dkonigsberg/nestronic/docs/render-1.png

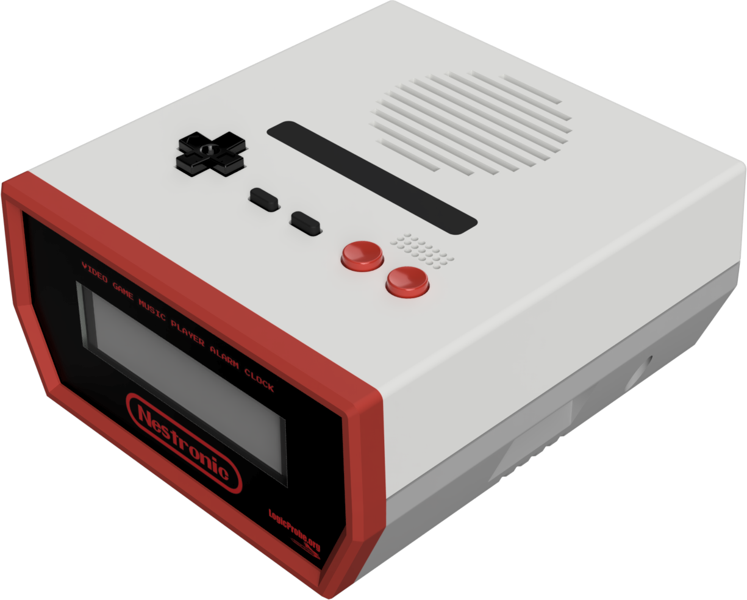
docs/render-1.png
