dkonigsberg/nestronic/docs/render-2.png

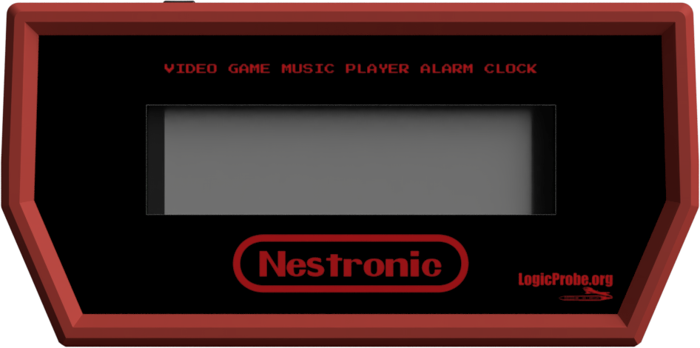
docs/render-2.png
