dkonigsberg/nestronic/docs/render-3.png

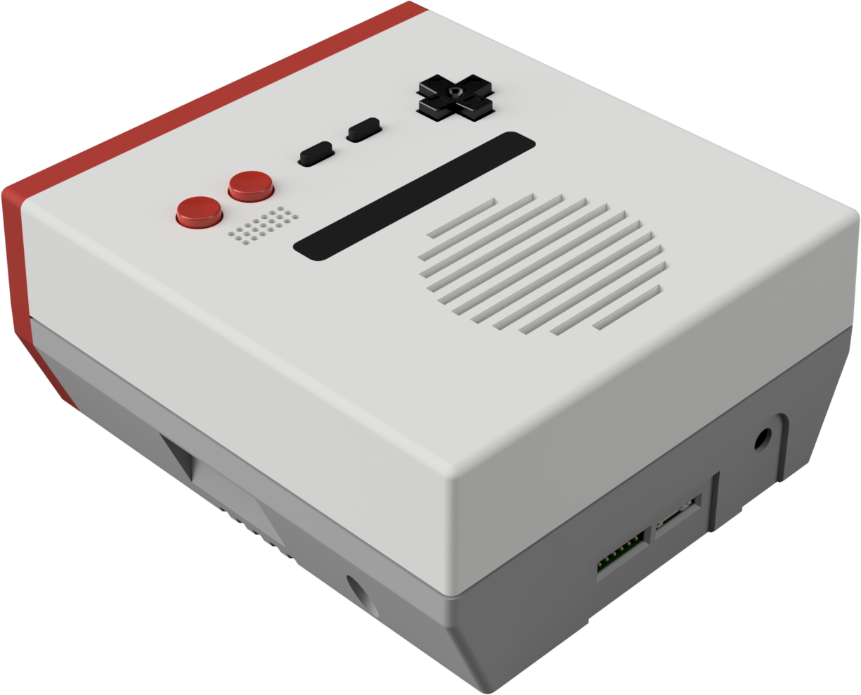
docs/render-3.png
