dkonigsberg/nestronic/docs/render-4.png

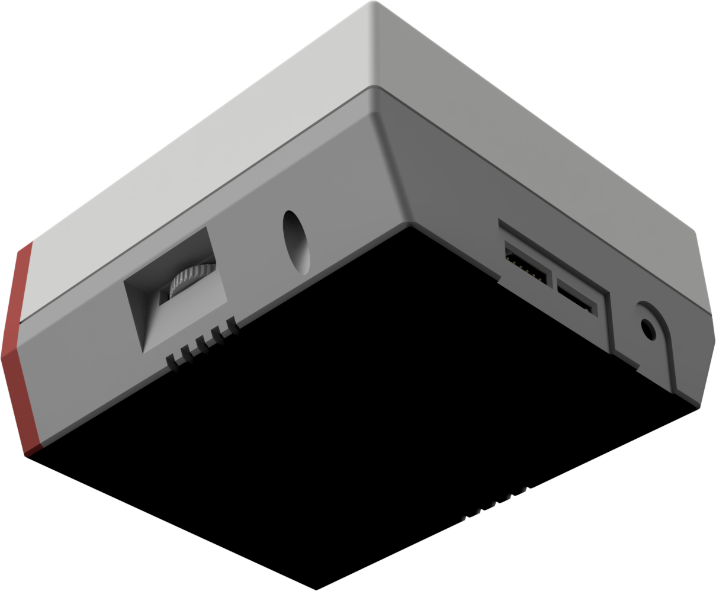
docs/render-4.png
