dkonigsberg/nestronic/hardware/3d_models/CUI_PJ-102AH.step

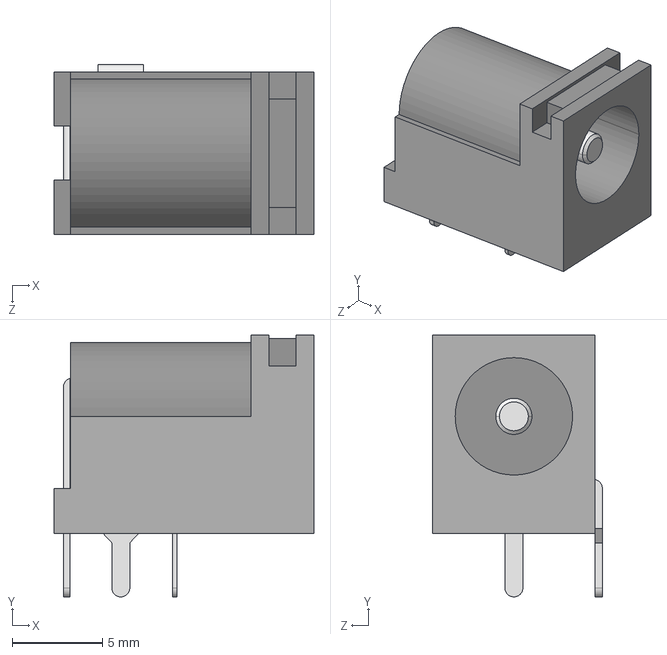
[picture p37: CAD file, 2018-06-15]
hardware/3d_models/CUI_PJ-102AH.step
14.4 x 14.5 x 9.40 mm
