dkonigsberg/nestronic/models/button_ab.step

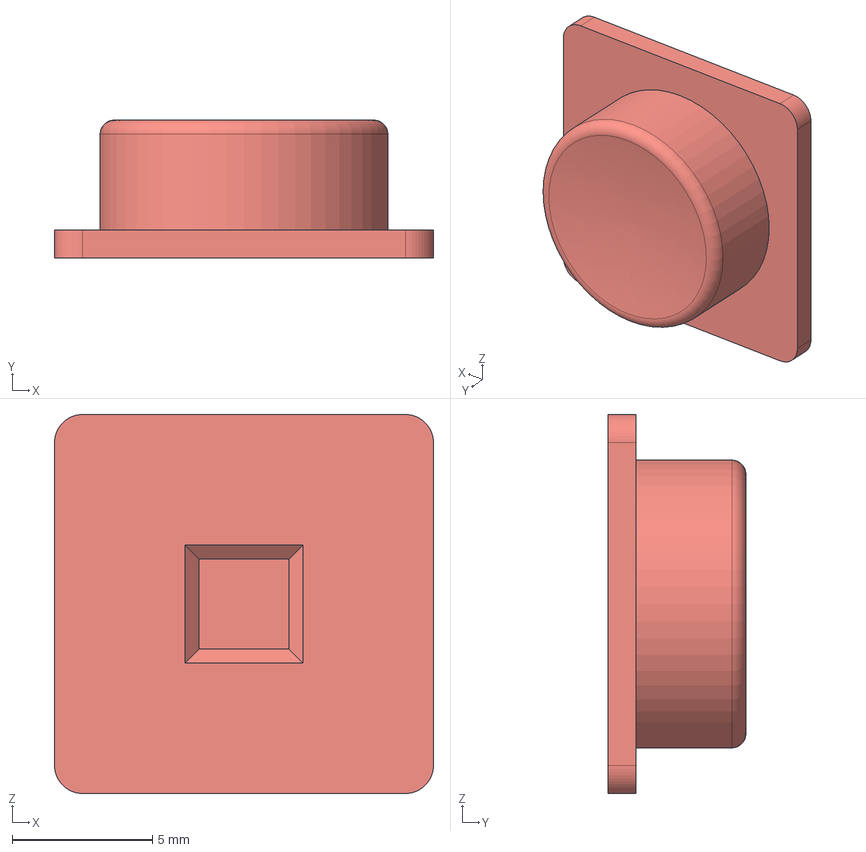
[picture p38: CAD file, 2018-06-17]
models/button_ab.step
13.5 x 4.91 x 13.5 mm
