dkonigsberg/nestronic/hardware/3d_models/SLP4016P16_1.6x4mm_P0.5mm.step

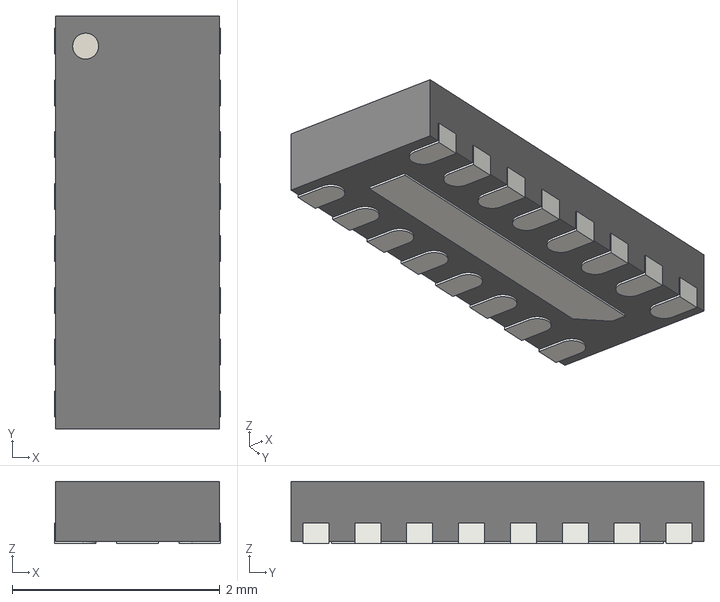
[picture p39: CAD file, 2018-06-15]
hardware/3d_models/SLP4016P16_1.6x4mm_P0.5mm.step
1.60 x 3.98 x 0.6 mm
