dkonigsberg/nestronic/models/button_4way.step

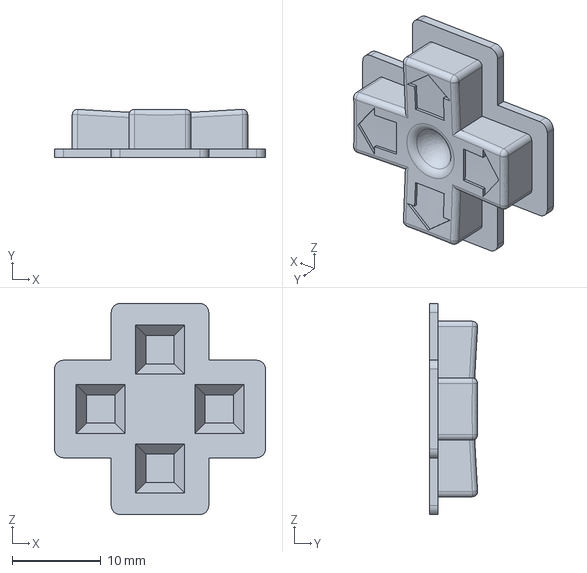
[picture p40: CAD file, 2018-06-17]
models/button_4way.step
23.8 x 5.45 x 23.8 mm
