dkonigsberg/nestronic/hardware/3d_models/R-78E-0-5.step

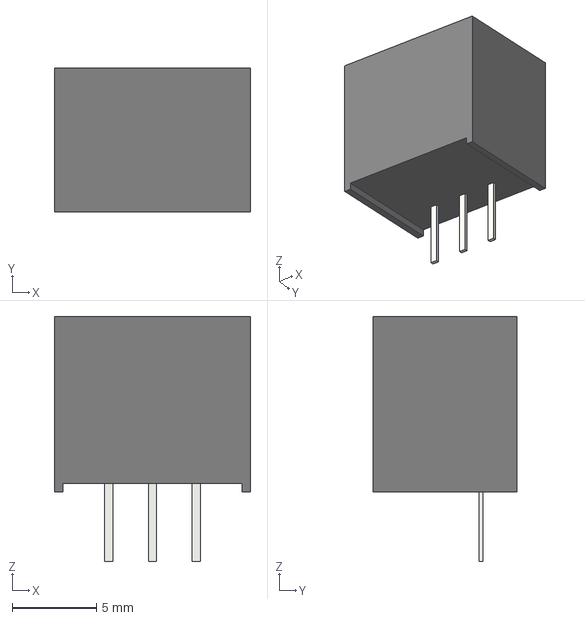
[picture p41: CAD file, 2018-06-15]
hardware/3d_models/R-78E-0-5.step
11.6 x 8.50 x 14.5 mm
