dkonigsberg/nestronic/models/button_select.step

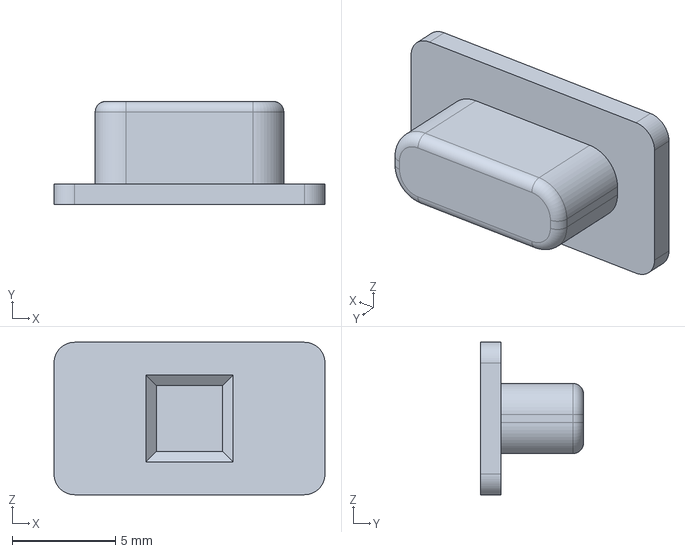
[picture p42: CAD file, 2018-06-17]
models/button_select.step
13.2 x 5.00 x 7.40 mm
