dkonigsberg/nestronic/hardware/3d_models/P090S-04F15AR1MEG.stp

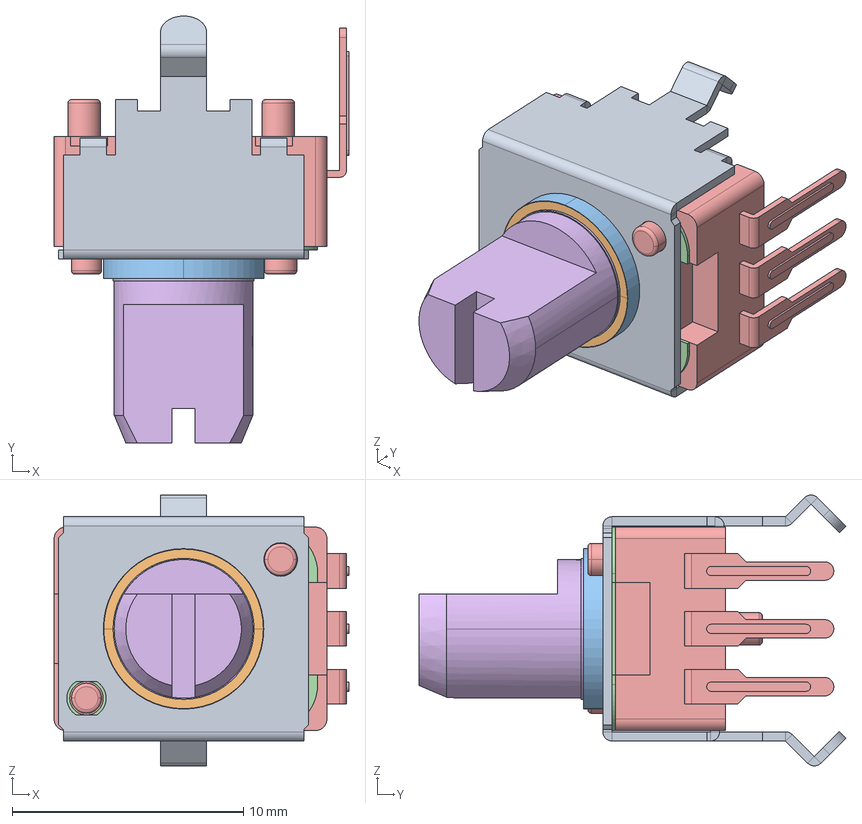
[picture p43: CAD file, 2018-06-15]
hardware/3d_models/P090S-04F15AR1MEG.stp
12.8 x 18.5 x 11.7 mm
12638-1-L15F
