dkonigsberg/nestronic/models/thumbwheel.step

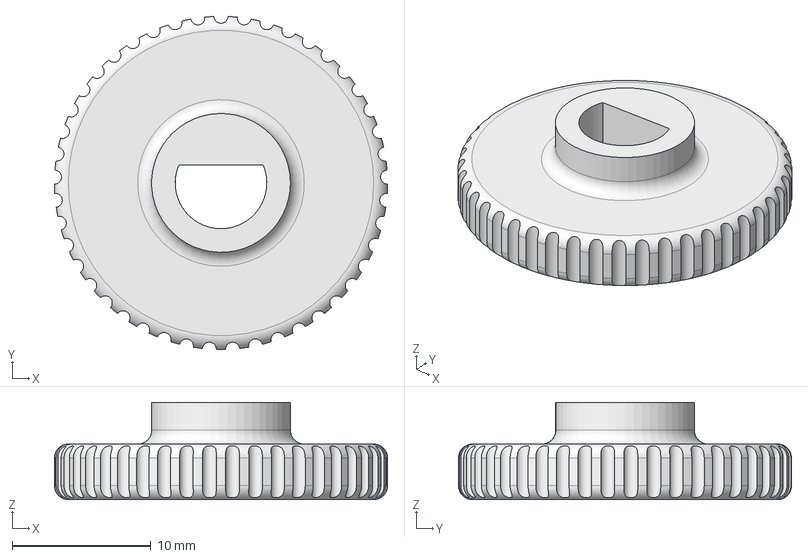
[picture p44: CAD file, 2018-06-15]
models/thumbwheel.step
24.0 x 24.0 x 7.00 mm
