dkonigsberg/nestronic/hardware/3d_models/TSL251R.step

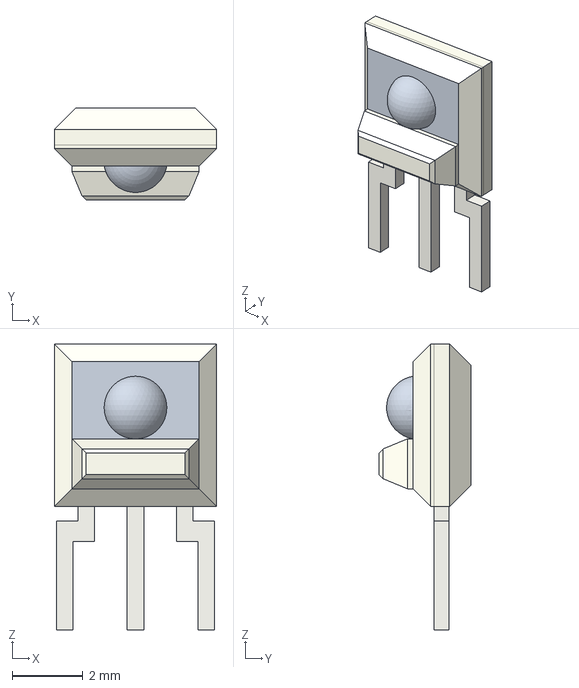
[picture p45: CAD file, 2018-06-15]
hardware/3d_models/TSL251R.step
4.60 x 2.60 x 8.10 mm
