dkonigsberg/nestronic/software/esp32/main/display_assets.c

#include "display_assets.h"

#define nestronic_width 256
#define nestronic_height 64
static uint8_t nestronic_bits[] = {
   0x00, 0x00, 0x00, 0xf0, 0xff, 0xff, 0xff, 0xff, 0xff, 0xff, 0xff, 0xff,
   0xff, 0xff, 0xff, 0xff, 0xff, 0xff, 0xff, 0xff, 0xff, 0xff, 0xff, 0xff,
   0xff, 0xff, 0xff, 0xff, 0x0f, 0x00, 0x00, 0x00, 0x00, 0x00, 0x80, 0xff,
   0xff, 0xff, 0xff, 0xff, 0xff, 0xff, 0xff, 0xff, 0xff, 0xff, 0xff, 0xff,
   0xff, 0xff, 0xff, 0xff, 0xff, 0xff, 0xff, 0xff, 0xff, 0xff, 0xff, 0xff,
   0xff, 0x01, 0x00, 0x00, 0x00, 0x00, 0xf0, 0xff, 0xff, 0xff, 0xff, 0xff,
   0xff, 0xff, 0xff, 0xff, 0xff, 0xff, 0xff, 0xff, 0xff, 0xff, 0xff, 0xff,
   0xff, 0xff, 0xff, 0xff, 0xff, 0xff, 0xff, 0xff, 0xff, 0x0f, 0x00, 0x00,
   0x00, 0x00, 0xfc, 0xff, 0xff, 0xff, 0xff, 0xff, 0xff, 0xff, 0xff, 0xff,
   0xff, 0xff, 0xff, 0xff, 0xff, 0xff, 0xff, 0xff, 0xff, 0xff, 0xff, 0xff,
   0xff, 0xff, 0xff, 0xff, 0xff, 0x3f, 0x00, 0x00, 0x00, 0x00, 0xff, 0xff,
   0xff, 0xff, 0xff, 0xff, 0xff, 0xff, 0xff, 0xff, 0xff, 0xff, 0xff, 0xff,
   0xff, 0xff, 0xff, 0xff, 0xff, 0xff, 0xff, 0xff, 0xff, 0xff, 0xff, 0xff,
   0xff, 0xff, 0x00, 0x00, 0x00, 0xc0, 0xff, 0xff, 0xff, 0xff, 0xff, 0xff,
   0xff, 0xff, 0xff, 0xff, 0xff, 0xff, 0xff, 0xff, 0xff, 0xff, 0xff, 0xff,
   0xff, 0xff, 0xff, 0xff, 0xff, 0xff, 0xff, 0xff, 0xff, 0xff, 0x03, 0x00,
   0x00, 0xe0, 0xff, 0xff, 0xff, 0xff, 0xff, 0xff, 0xff, 0xff, 0xff, 0xff,
   0xff, 0xff, 0xff, 0xff, 0xff, 0xff, 0xff, 0xff, 0xff, 0xff, 0xff, 0xff,
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
   0xc3, 0x0f, 0x30, 0xc3, 0x0f, 0x30, 0xef, 0x03, 0x3c, 0xef, 0xff, 0x3d,
   0xec, 0xff, 0x0d, 0x0c, 0x00, 0x0c, 0x3c, 0x00, 0x0f, 0x3c, 0x00, 0x0f,
   0xf0, 0xcc, 0x03, 0xf0, 0xcc, 0x03, 0xc0, 0xff, 0x00, 0xc0, 0xff, 0x00 };

uint8_t display_asset_get(asset_info_t *asset_info, asset_name_t asset_name)
{
    switch (asset_name) {
    case ASSET_NESTRONIC:
        *asset_info = (asset_info_t) {
            .bits = nestronic_bits,
            .height = nestronic_height,
            .width = nestronic_width
        };
        return 1;
    case ASSET_SEG_A:
        *asset_info = (asset_info_t) {
            .bits = seg_a_bits,
            .height = seg_a_height,
            .width = seg_a_width
        };
        return 1;
    case ASSET_SEG_B:
        *asset_info = (asset_info_t) {
            .bits = seg_b_bits,
            .height = seg_b_height,
            .width = seg_b_width
        };
        return 1;
    case ASSET_SEG_C:
        *asset_info = (asset_info_t) {
            .bits = seg_c_bits,
            .height = seg_c_height,
            .width = seg_c_width
        };
        return 1;
    case ASSET_SEG_D:
        *asset_info = (asset_info_t) {
            .bits = seg_d_bits,
            .height = seg_d_height,
            .width = seg_d_width
        };
        return 1;
    case ASSET_SEG_E:
        *asset_info = (asset_info_t) {
            .bits = seg_e_bits,
            .height = seg_e_height,
            .width = seg_e_width
        };
        return 1;
    case ASSET_SEG_F:
        *asset_info = (asset_info_t) {
            .bits = seg_f_bits,
            .height = seg_f_height,
            .width = seg_f_width
        };
        return 1;
    case ASSET_SEG_G:
        *asset_info = (asset_info_t) {
            .bits = seg_g_bits,
            .height = seg_g_height,
            .width = seg_g_width
        };
        return 1;
    case ASSET_SEG_SEP:
        *asset_info = (asset_info_t) {
            .bits = seg_sep_bits,
            .height = seg_sep_height,
            .width = seg_sep_width
        };
        return 1;
    case ASSET_TSEG_CH_A:
        *asset_info = (asset_info_t) {
            .bits = tseg_ch_a_bits,
            .height = tseg_ch_a_height,
            .width = tseg_ch_a_width
        };
        return 1;
    case ASSET_TSEG_CH_P:
        *asset_info = (asset_info_t) {
            .bits = tseg_ch_p_bits,
            .height = tseg_ch_p_height,
            .width = tseg_ch_p_width
        };
        return 1;
    case ASSET_TSEG_CH_M:
        *asset_info = (asset_info_t) {
            .bits = tseg_ch_m_bits,
            .height = tseg_ch_m_height,
            .width = tseg_ch_m_width
        };
        return 1;
    case ASSET_CLOCK_ICON:
        *asset_info = (asset_info_t) {
            .bits = clock_icon_bits,
            .height = clock_icon_height,
            .width = clock_icon_width
        };
        return 1;
    case ASSET_SNOOZE_ICON:
        *asset_info = (asset_info_t) {
            .bits = snooze_icon_bits,
            .height = snooze_icon_height,
            .width = snooze_icon_width
        };
        return 1;
    default:
        return 0;
    }
}
